nekoewen/lexicon/case/IMG_7951.jpeg

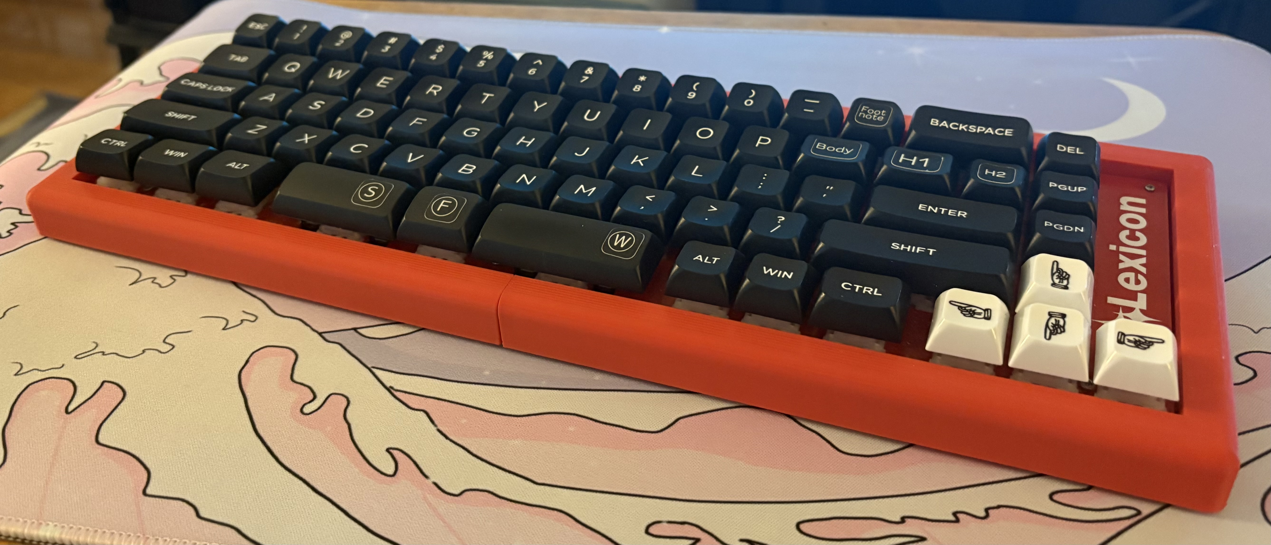
case/IMG_7951.jpeg
