nekoewen/lexicon/case/IMG_7952.jpeg

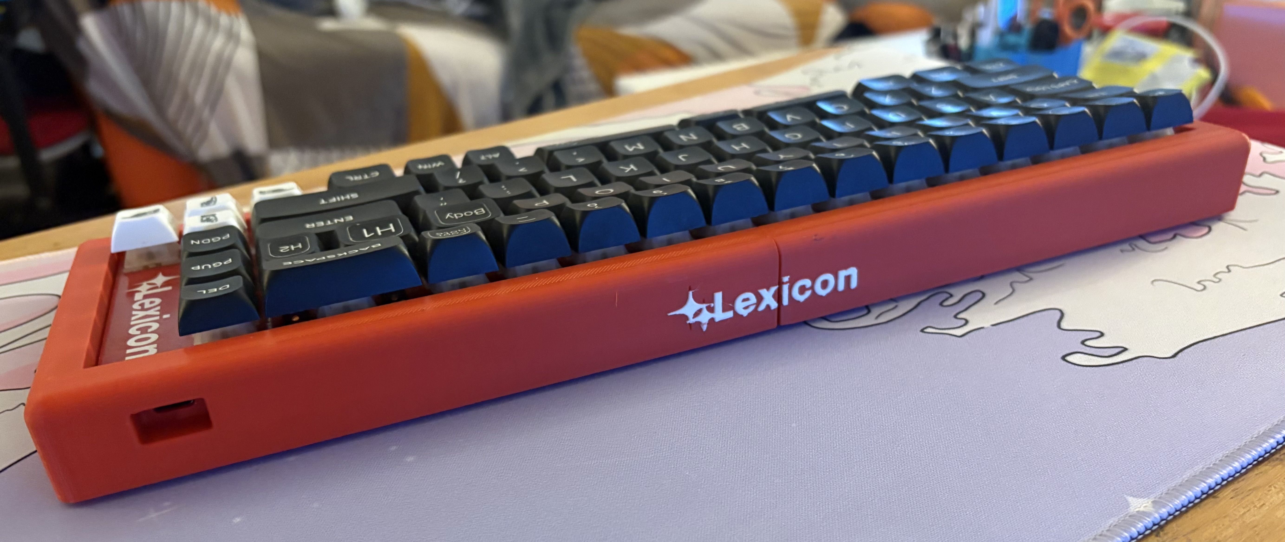
case/IMG_7952.jpeg
